mmdoogie/hello-badge/src/epdpaint.cpp

/**
 *  @filename   :   epdpaint.cpp
 *  @brief      :   Paint tools
 *  @author     :   Yehui from Waveshare
 *  
 *  Copyright (C) Waveshare     September 9 2017
 *
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
 * THE SOFTWARE IS PROVIDED "AS IS", WITHOUT WARRANTY OF ANY KIND, EXPRESS OR
 * IMPLIED, INCLUDING BUT NOT LIMITED TO THE WARRANTIES OF MERCHANTABILITY,
 * FITNESS OR A PARTICULAR PURPOSE AND NONINFRINGEMENT. IN NO EVENT SHALL THE
 * AUTHORS OR COPYRIGHT HOLDERS BE LIABLE FOR ANY CLAIM, DAMAGES OR OTHER
 * LIABILITY WHETHER IN AN ACTION OF CONTRACT, TORT OR OTHERWISE, ARISING FROM,
 * OUT OF OR IN CONNECTION WITH THE SOFTWARE OR THE USE OR OTHER DEALINGS IN
 * THE SOFTWARE.
 */

#include "epdpaint.h"

Paint::Paint(unsigned char* image, int width, int height) {
    this->rotate = ROTATE_0;
    this->invert = INVERT;
    this->image = image;
    /* 1 byte = 8 pixels, so the width should be the multiple of 8 */
    this->width = width % 8 ? width + 8 - (width % 8) : width;
    this->height = height;
}

Paint::~Paint() {
}

/**
 *  @brief: clear the image
 */
void Paint::Clear(int colored) {
    for (int x = 0; x < this->width; x++) {
        for (int y = 0; y < this->height; y++) {
            DrawAbsolutePixel(x, y, colored);
        }
    }
}

/**
 *  @brief: this draws a pixel by absolute coordinates.
 *          this function won't be affected by the rotate parameter.
 */
void Paint::DrawAbsolutePixel(int x, int y, int colored) {
    if (x < 0 || x >= this->width || y < 0 || y >= this->height) {
        return;
    }
    if (this->invert) {
        if (colored) {
            image[(x + y * this->width) / 8] |= 0x80 >> (x % 8);
        } else {
            image[(x + y * this->width) / 8] &= ~(0x80 >> (x % 8));
        }
    } else {
        if (colored) {
            image[(x + y * this->width) / 8] &= ~(0x80 >> (x % 8));
        } else {
            image[(x + y * this->width) / 8] |= 0x80 >> (x % 8);
        }
    }
}

/**
 *  @brief: Getters and Setters
 */
unsigned char* Paint::GetImage(void) {
    return this->image;
}

int Paint::GetWidth(void) {
    return this->width;
}

void Paint::SetWidth(int width) {
    this->width = width % 8 ? width + 8 - (width % 8) : width;
}

int Paint::GetHeight(void) {
    return this->height;
}

void Paint::SetHeight(int height) {
    this->height = height;
}

int Paint::GetRotate(void) {
    return this->rotate;
}

void Paint::SetRotate(int rotate) {
    this->rotate = rotate;
}

int Paint::GetInvert(void) {
    return this->invert;
}

void Paint::SetInvert(int invert) {
    this->invert = invert;
}

/**
 *  @brief: this draws a pixel by the coordinates
 */
void Paint::DrawPixel(int x, int y, int colored) {
    int point_temp;
    if (this->rotate == ROTATE_0) {
        if(x < 0 || x >= this->width || y < 0 || y >= this->height) {
            return;
        }
        DrawAbsolutePixel(x, y, colored);
    } else if (this->rotate == ROTATE_90) {
        if(x < 0 || x >= this->height || y < 0 || y >= this->width) {
          return;
        }
        point_temp = x;
        x = this->width - y;
        y = point_temp;
        DrawAbsolutePixel(x, y, colored);
    } else if (this->rotate == ROTATE_180) {
        if(x < 0 || x >= this->width || y < 0 || y >= this->height) {
          return;
        }
        x = this->width - x;
        y = this->height - y;
        DrawAbsolutePixel(x, y, colored);
    } else if (this->rotate == ROTATE_270) {
        if(x < 0 || x >= this->height || y < 0 || y >= this->width) {
          return;
        }
        point_temp = x;
        x = y;
        y = this->height - point_temp;
        DrawAbsolutePixel(x, y, colored);
    }
}

Paint::point_t Paint::GetAbsoluteLocation(int x, int y) {
    point_t ret;
    ret.x = -1;
    ret.y = -1;

    if (this->rotate == ROTATE_0) {
        if(x < 0 || x >= this->width || y < 0 || y >= this->height) {
            return ret;
        }
        ret.x = x;
        ret.y = y;
    } else if (this->rotate == ROTATE_90) {
        if(x < 0 || x >= this->height || y < 0 || y >= this->width) {
          return ret;
        }
        ret.x = this->width - y;
        ret.y = x;
    } else if (this->rotate == ROTATE_180) {
        if(x < 0 || x >= this->width || y < 0 || y >= this->height) {
          return ret;
        }
        ret.x = this->width - x;
        ret.y = this->height - y;
    } else if (this->rotate == ROTATE_270) {
        if(x < 0 || x >= this->height || y < 0 || y >= this->width) {
          return ret;
        }
        ret.x = y;
        ret.y = this->height - x;
    }

    return ret;
}

/**
 *  @brief: this draws a charactor on the frame buffer but not refresh
 */
void Paint::DrawCharAt(int x, int y, char ascii_char, MonoBitFont* font, int colored) {
    int i, j;

    uint8_t *ptr = font->getCharData(ascii_char);

    for (j = 0; j < font->getCharHeight(); j++) {
        for (i = 0; i < font->getCharWidth(ascii_char); i++) {
            if (*ptr & (0x80 >> (i % 8))) {
                DrawPixel(x + i, y + j, colored);
            }
            if (i % 8 == 7) {
                ptr++;
            }
        }
        if (font->getCharWidth(ascii_char) % 8 != 0) {
            ptr++;
        }
    }
}

/**
*  @brief: this displays a string on the frame buffer but not refresh
*/
void Paint::DrawStringAt(int x, int y, const char* text, MonoBitFont* font, int colored) {
    const char* p_text = text;
    unsigned int counter = 0;
    int refcolumn = x;
    
    /* Send the string character by character on EPD */
    while (*p_text != 0) {
        /* Display one character on EPD */
        DrawCharAt(refcolumn, y, *p_text, font, colored);
        /* Decrement the column position by 16 */
        refcolumn += font->getCharWidth(*p_text) + font->getSpacing();
        /* Point on the next character */
        p_text++;
        counter++;
    }
}

void Paint::DrawStringCenteredIn(int x, int y, int width, int height, const char* text, MonoBitFont* font, int colored) {
    int strWidth = font->getStringWidth(text);
    int strHeight = font->getCharHeight();

    DrawStringAt(x + (width - strWidth) / 2, y + (height - strHeight) / 2, text, font, colored);
}

void Paint::DrawStringCenteredAt(int x, int y, const char* text, MonoBitFont* font, int colored) {
    int strWidth = font->getStringWidth(text);
    int strHeight = font->getCharHeight();

    DrawStringAt(x - strWidth / 2, y - strHeight / 2, text, font, colored);
}

/**
*  @brief: this draws a line on the frame buffer
*/
void Paint::DrawLine(int x0, int y0, int x1, int y1, int colored) {
    /* Bresenham algorithm */
    int dx = x1 - x0 >= 0 ? x1 - x0 : x0 - x1;
    int sx = x0 < x1 ? 1 : -1;
    int dy = y1 - y0 <= 0 ? y1 - y0 : y0 - y1;
    int sy = y0 < y1 ? 1 : -1;
    int err = dx + dy;

    while((x0 != x1) && (y0 != y1)) {
        DrawPixel(x0, y0 , colored);
        if (2 * err >= dy) {     
            err += dy;
            x0 += sx;
        }
        if (2 * err <= dx) {
            err += dx; 
            y0 += sy;
        }
    }
}

/**
*  @brief: this draws a horizontal line on the frame buffer
*/
void Paint::DrawHorizontalLine(int x, int y, int line_width, int colored) {
    int i;
    for (i = x; i < x + line_width; i++) {
        DrawPixel(i, y, colored);
    }
}

/**
*  @brief: this draws a vertical line on the frame buffer
*/
void Paint::DrawVerticalLine(int x, int y, int line_height, int colored) {
    int i;
    for (i = y; i < y + line_height; i++) {
        DrawPixel(x, i, colored);
    }
}

/**
*  @brief: this draws a rectangle
*/
void Paint::DrawRectangle(int x0, int y0, int x1, int y1, int colored) {
    int min_x, min_y, max_x, max_y;
    min_x = x1 > x0 ? x0 : x1;
    max_x = x1 > x0 ? x1 : x0;
    min_y = y1 > y0 ? y0 : y1;
    max_y = y1 > y0 ? y1 : y0;
    
    DrawHorizontalLine(min_x, min_y, max_x - min_x + 1, colored);
    DrawHorizontalLine(min_x, max_y, max_x - min_x + 1, colored);
    DrawVerticalLine(min_x, min_y, max_y - min_y + 1, colored);
    DrawVerticalLine(max_x, min_y, max_y - min_y + 1, colored);
}

/**
*  @brief: this draws a filled rectangle
*/
void Paint::DrawFilledRectangle(int x0, int y0, int x1, int y1, int colored) {
    int min_x, min_y, max_x, max_y;
    int i;
    min_x = x1 > x0 ? x0 : x1;
    max_x = x1 > x0 ? x1 : x0;
    min_y = y1 > y0 ? y0 : y1;
    max_y = y1 > y0 ? y1 : y0;
    
    for (i = min_x; i <= max_x; i++) {
      DrawVerticalLine(i, min_y, max_y - min_y + 1, colored);
    }
}

void Paint::DrawFilledRoundedRectangle(int x0, int y0, int x1, int y1, int radius, int colored) {
    int min_x, min_y, max_x, max_y;
    min_x = x1 > x0 ? x0 : x1;
    max_x = x1 > x0 ? x1 : x0;
    min_y = y1 > y0 ? y0 : y1;
    max_y = y1 > y0 ? y1 : y0;
    
    DrawFilledCircle(min_x + radius, min_y + radius, radius, colored);
    DrawFilledCircle(min_x + radius, max_y - radius, radius, colored);
    DrawFilledCircle(max_x - radius, min_y + radius, radius, colored);
    DrawFilledCircle(max_x - radius, max_y - radius, radius, colored);
    DrawFilledRectangle(min_x + radius, min_y, max_x - radius, max_y, colored);
    DrawFilledRectangle(min_x, min_y + radius, min_x + radius, max_y - radius, colored);
    DrawFilledRectangle(max_x - radius, min_y + radius, max_x, max_y - radius, colored);
}

/**
*  @brief: this draws a circle
*/
void Paint::DrawCircle(int x, int y, int radius, int colored) {
    /* Bresenham algorithm */
    int x_pos = -radius;
    int y_pos = 0;
    int err = 2 - 2 * radius;
    int e2;

    do {
        DrawPixel(x - x_pos, y + y_pos, colored);
        DrawPixel(x + x_pos, y + y_pos, colored);
        DrawPixel(x + x_pos, y - y_pos, colored);
        DrawPixel(x - x_pos, y - y_pos, colored);
        e2 = err;
        if (e2 <= y_pos) {
            err += ++y_pos * 2 + 1;
            if(-x_pos == y_pos && e2 <= x_pos) {
              e2 = 0;
            }
        }
        if (e2 > x_pos) {
            err += ++x_pos * 2 + 1;
        }
    } while (x_pos <= 0);
}

/**
*  @brief: this draws a filled circle
*/
void Paint::DrawFilledCircle(int x, int y, int radius, int colored) {
    /* Bresenham algorithm */
    int x_pos = -radius;
    int y_pos = 0;
    int err = 2 - 2 * radius;
    int e2;

    do {
        DrawPixel(x - x_pos, y + y_pos, colored);
        DrawPixel(x + x_pos, y + y_pos, colored);
        DrawPixel(x + x_pos, y - y_pos, colored);
        DrawPixel(x - x_pos, y - y_pos, colored);
        DrawHorizontalLine(x + x_pos, y + y_pos, 2 * (-x_pos) + 1, colored);
        DrawHorizontalLine(x + x_pos, y - y_pos, 2 * (-x_pos) + 1, colored);
        e2 = err;
        if (e2 <= y_pos) {
            err += ++y_pos * 2 + 1;
            if(-x_pos == y_pos && e2 <= x_pos) {
                e2 = 0;
            }
        }
        if(e2 > x_pos) {
            err += ++x_pos * 2 + 1;
        }
    } while(x_pos <= 0);
}

void Paint::BitBlt(int x, int y, int width, int height, const uint8_t* img) {
    int rowSize = (width / 8) + ((width % 8) ? 1 : 0);

    for (int dy = 0; dy < height; dy++) {
        for (int dx = 0; dx < width; dx++) {
            unsigned char b = img[rowSize * dy + (dx/8)];
            DrawPixel(x+dx, y+dy, (b & (1<<(7-(dx%8)))) ? 1 : 0);
        }
    }
}

/* END OF FILE */
